swiftrax/Trifecta/Case/Case_Archived/Laser Files/Rev 2.0/DXF/readme.md

Amount of layers for a laser cut case
- Use 3mm acrylic for all layers
- Midlayers x3
- Hi Pro layers x2
- Plate x1 1.5mm Aluminum
- Feet x1 per size
- Use 9mm M3 threaded hex standoffs
- Use M3 screws of appropriate sizes
