swiftrax/Trifecta/Images_Renders/Final Renders/AluExplode.png

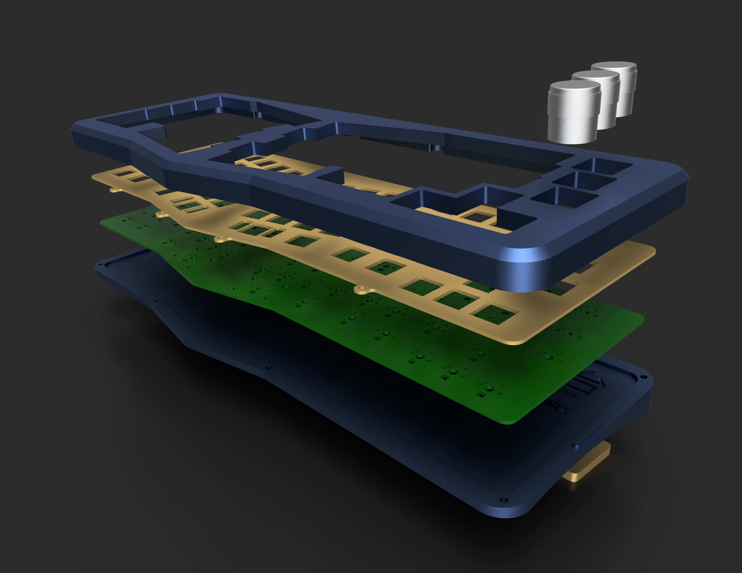
Images_Renders/Final Renders/AluExplode.png
