swiftrax/Trifecta/Images_Renders/Final Renders/AluSide.png

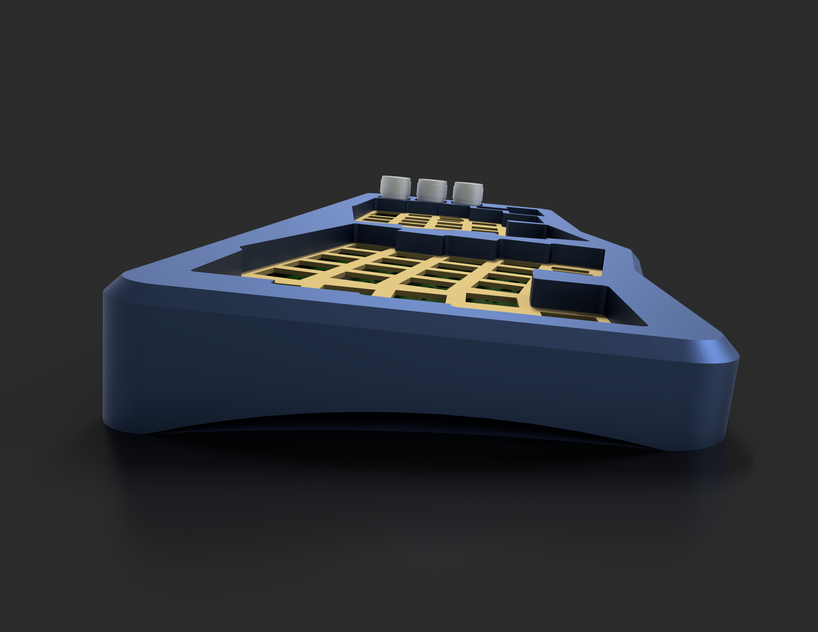
Images_Renders/Final Renders/AluSide.png
