swiftrax/Trifecta/Images_Renders/Final Renders/BlackISO.png

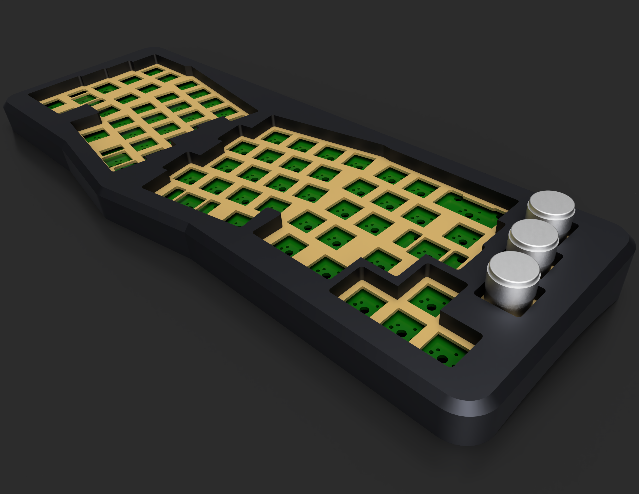
Images_Renders/Final Renders/BlackISO.png
