swiftrax/Trifecta/Images_Renders/Final Renders/Detail.png

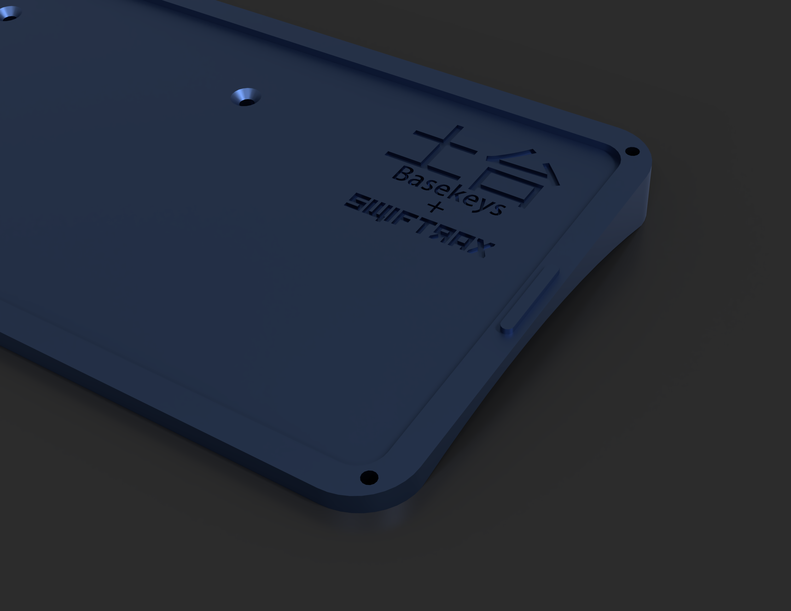
Images_Renders/Final Renders/Detail.png
