swiftrax/Trifecta/Images_Renders/Final Renders/PCISO.png

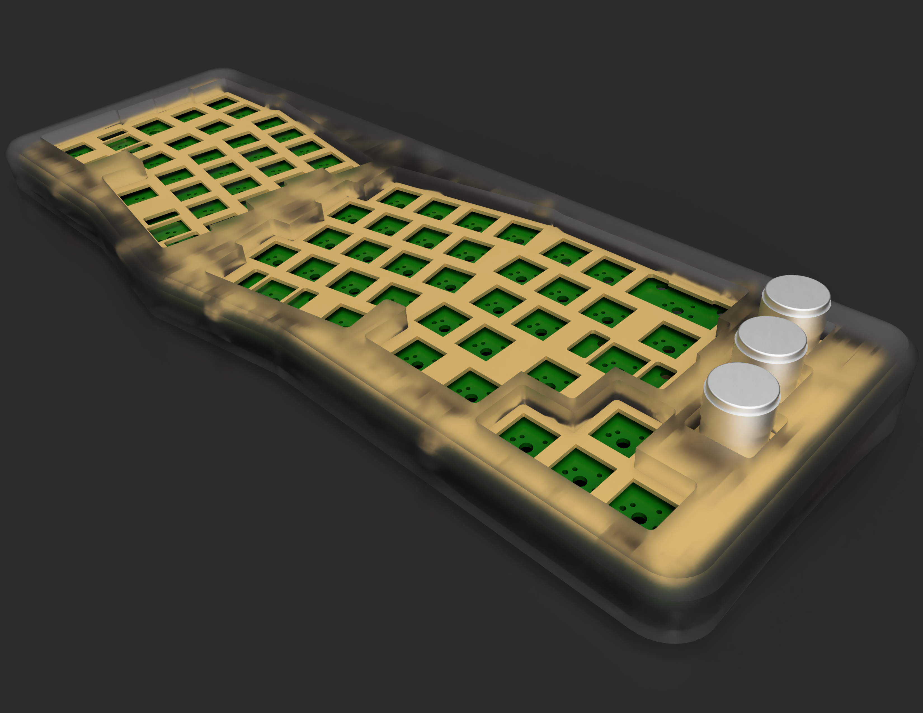
Images_Renders/Final Renders/PCISO.png
